skygadgetsab/rchub/RCHub X/STL/RCHub X - Spacer Back RPi 5.stl

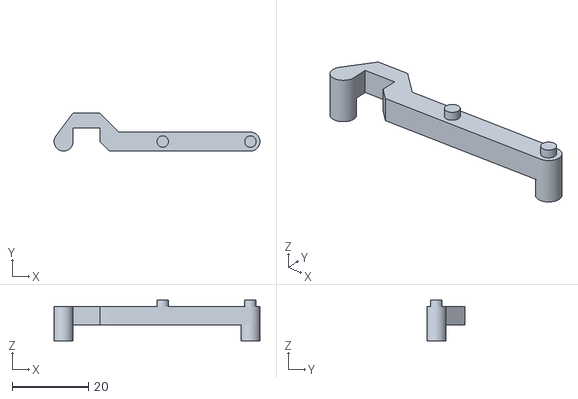
[picture p17: CAD file, 2026-10-03]
RCHub X/STL/RCHub X - Spacer Back RPi 5.stl
54.0 x 10.0 x 10.7
